trdenton/mrgtimer_firmware/mrgtimer_firmware/lcd.cpp

#include "Arduino.h"
#include "DFRobot_RGBLCD1602.h"

static DFRobot_RGBLCD1602 lcd(16, 2); // 16 characters x 2 lines

// assumes cursor is in the correct position
// converts t to MM:SS.sss
// assumes we are receiving ticks at 32768 kHz
void lcd_print_time(long unsigned int t)
{
  // 32768 counts is one second
  // 32.768 is one millisecond
  int minutes = t / (32768*60);
  int seconds = (t/ 32768)%60;
  int milliseconds = ((t*1000)/32768)%1000;
  if (minutes < 10)
    lcd.print("0");
  lcd.print(minutes); lcd.print(":"); 

  if (seconds < 10)
    lcd.print("0");
  lcd.print(seconds); lcd.print(".");

  if (milliseconds < 100)
    lcd.print("0");
  if (milliseconds < 10)
    lcd.print("0");
  lcd.print(milliseconds);
}

// used for printing elapsed time while race is on
void lcd_elapsed(int row, long unsigned int t) {
  lcd.setCursor(0, row);
  lcd_print_time(t);
}

void lcd_init() 
{
  lcd.init();
}

void lcd_clear()
{
  lcd.clear();
}

void lcd_message(const char* str)
{
  static char last[16] = "";
  // basic mechanism to not spam LCD with
  // same message

  if ( strncmp(str,last,16) ) {
    lcd.clear();
    lcd.setCursor(0,1);
    lcd.print(str);
  }

  strncpy(last,str,16);
}

// print the result for lane (lane 0 is row 0, lane 1 is row 1)
void lcd_result(int lane, long unsigned int ms) {
  lcd.setCursor(0,lane);
  lcd.print("L"); lcd.print(lane+1); lcd.print(": "); lcd_print_time(ms);
}
